V-Socrates/RaspiGuard/Documentation/RaspiGuard OACETT TR Checklist.png

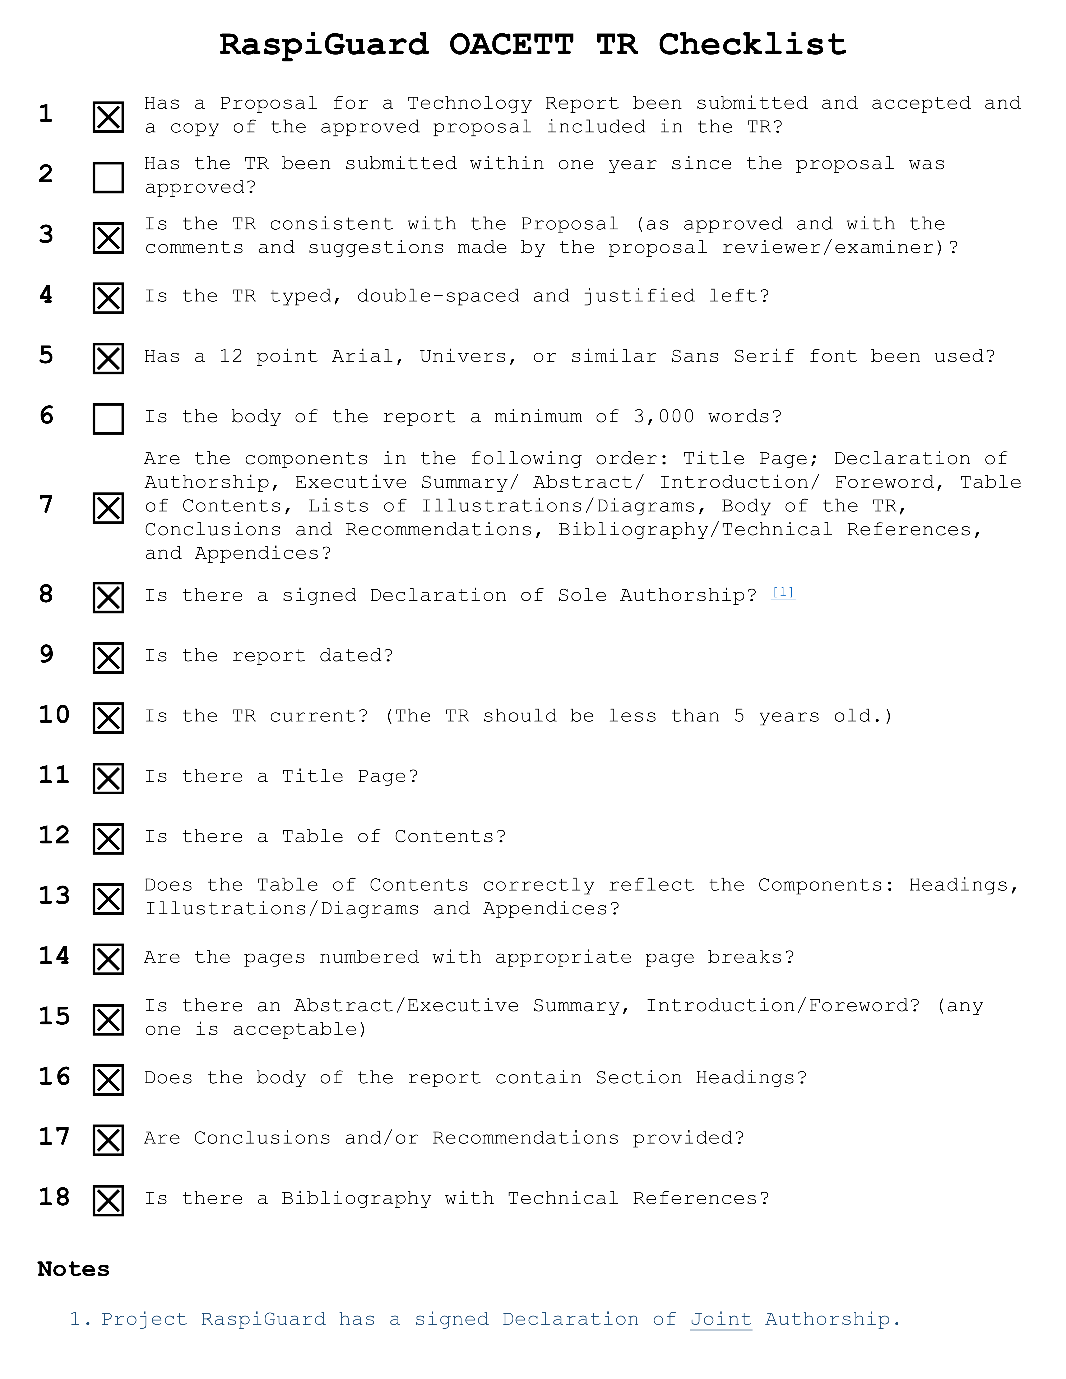
Documentation/RaspiGuard OACETT TR Checklist.png
